shufps/qaxe/nerdqaxe++/nerdqaxe++/3d/csg95472.step

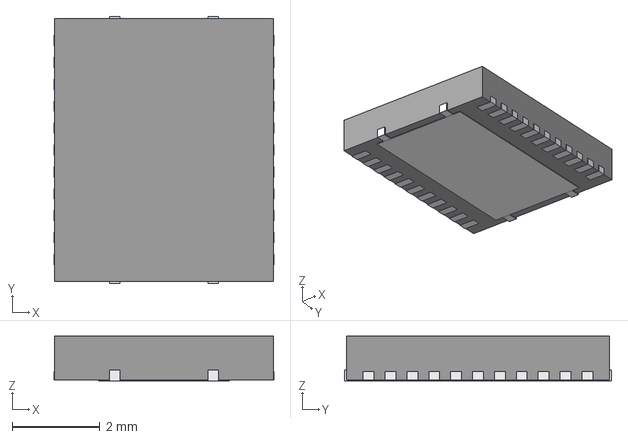
[picture p17: CAD file, 2024-11-11]
nerdqaxe++/nerdqaxe++/3d/csg95472.step
5.02 x 6.10 x 1.02 mm
