shufps/qaxe/nerdqaxe++/nerdqaxe++/bm1366.kicad_sch

## KiCad design nerdqaxe++/nerdqaxe++/bm1366.kicad_sch (2026-01-11)

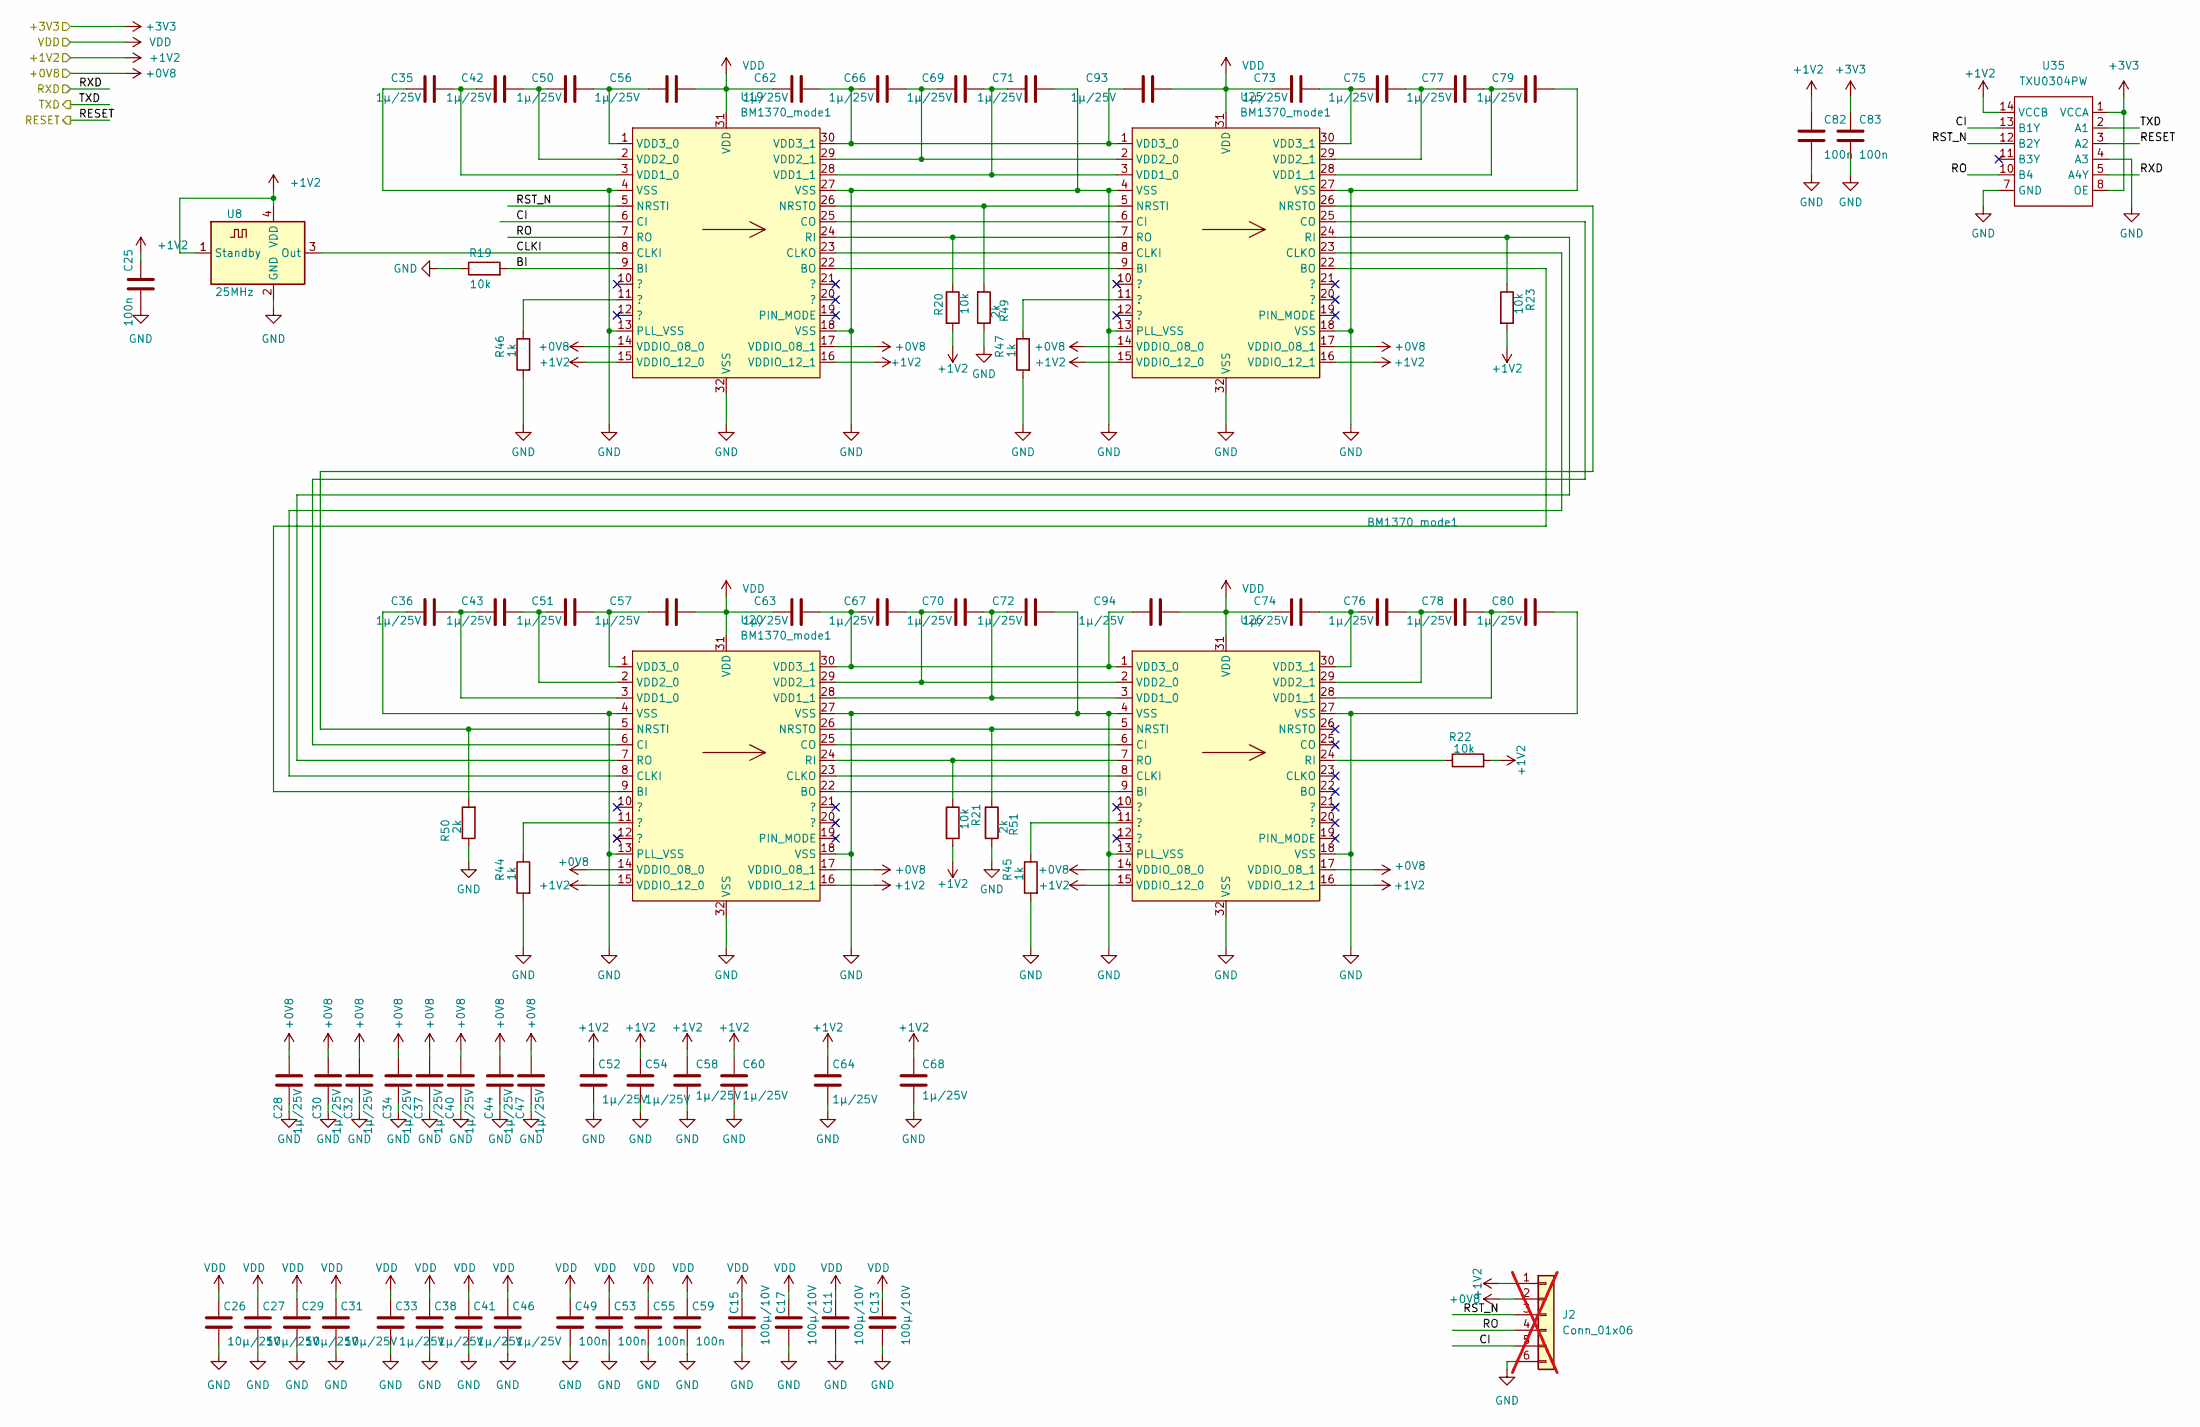
[picture p28: schematic bm1366.kicad_sch]

Parts:
C11, C13, C15, C17: 100µ/10V; C_1210_3225Metric
C25, C49, C53, C55, C59, C82, C83: 100n; C_0805_2012Metric
C26, C27, C29, C31: 10µ/25V; C_0805_2012Metric
C28, C30, C32, C33, C34, C35, C36, C37, C38, C40, C41, C42, C43, C44, C46, C47, C50, C51, C52, C54, C56, C57, C58, C60, C62, C63, C64, C66, C67, C68, C69, C70, C71, C72, C73, C74, C75, C76, C77, C78, C79, C80, C93, C94: 1µ/25V; C_0805_2012Metric
J2: Conn_01x06; PinHeader_1x06_P1.27mm_Vertical; not fitted
R19, R20, R21, R22, R23: 10k; R_0805_2012Metric
R44, R45, R46, R47: 1k; R_0805_2012Metric
R49, R50, R51: 2k; R_0805_2012Metric
U8: 25MHz; Oscillator_SMD_EuroQuartz_XO32-4Pin_3.2x2.5mm
U19, U20, U25, U26: BM1370_mode1; BM1370
U35: TXU0304PW; TSSOP-14_4.4x5mm_P0.65mm

Connections:
+0V8: C28.2, C30.2, C32.2, C34.2, C37.2, C40.2, C44.2, C47.2, J2.2, U19.14 (VDDIO_08_0), U19.17 (VDDIO_08_1), U20.14 (VDDIO_08_0), U20.17 (VDDIO_08_1), U25.14 (VDDIO_08_0), U25.17 (VDDIO_08_1), U26.14 (VDDIO_08_0), U26.17 (VDDIO_08_1)
+1V2: C25.1, C52.1, C54.1, C58.1, C60.1, C64.1, C68.1, C82.1, J2.1, R20.2, R21.2, R22.2, R23.2, U8.1 (Standby), U8.4 (VDD), U19.15 (VDDIO_12_0), U19.16 (VDDIO_12_1), U20.15 (VDDIO_12_0), U20.16 (VDDIO_12_1), U25.15 (VDDIO_12_0), U25.16 (VDDIO_12_1), U26.15 (VDDIO_12_0), U26.16 (VDDIO_12_1), U35.14 (VCCB)
+3V3: C83.1, U35.1 (VCCA), U35.8 (OE)
BI: R19.2, U19.9 (BI)
CI: J2.5, U19.6 (CI), U35.13 (B1Y)
CLKI: U8.3 (Out), U19.8 (CLKI)
GND: C11.2, C13.2, C15.2, C17.2, C25.2, C26.2, C27.2, C28.1, C29.2, C30.1, C31.2, C32.1, C33.2, C34.1, C35.1, C36.1, C37.1, C38.2, C40.1, C41.2, C44.1, C46.2, C47.1, C49.2, C52.2, C53.2, C54.2, C55.2, C58.2, C59.2, C60.2, C64.2, C68.2, C71.2, C72.2, C79.2, C80.2, C82.2, C83.2, J2.6, R19.1, R44.2, R45.2, R46.2, R47.2, R49.1, R50.1, R51.1, U8.2 (GND), U19.4 (VSS), U19.13 (PLL_VSS), U19.18 (VSS), U19.27 (VSS), U19.32 (VSS), U20.4 (VSS), U20.13 (PLL_VSS), U20.18 (VSS), U20.27 (VSS), U20.32 (VSS), U25.4 (VSS), U25.13 (PLL_VSS), U25.18 (VSS), U25.27 (VSS), U25.32 (VSS), U26.4 (VSS), U26.13 (PLL_VSS), U26.18 (VSS), U26.27 (VSS), U26.32 (VSS), U35.4 (A3), U35.7 (GND)
unnamed: C35.2, C42.1, U19.3 (VDD1_0)
unnamed: C36.2, C43.1, U20.3 (VDD1_0)
unnamed: C42.2, C50.1, U19.2 (VDD2_0)
unnamed: C43.2, C51.1, U20.2 (VDD2_0)
unnamed: C50.2, C56.1, U19.1 (VDD3_0)
unnamed: C51.2, C57.1, U20.1 (VDD3_0)
unnamed: C62.2, C66.1, C93.1, U19.30 (VDD3_1), U25.1 (VDD3_0)
unnamed: C63.2, C67.1, C94.1, U20.30 (VDD3_1), U26.1 (VDD3_0)
unnamed: C66.2, C69.1, U19.29 (VDD2_1), U25.2 (VDD2_0)
unnamed: C67.2, C70.1, U20.29 (VDD2_1), U26.2 (VDD2_0)
unnamed: C69.2, C71.1, U19.28 (VDD1_1), U25.3 (VDD1_0)
unnamed: C70.2, C72.1, U20.28 (VDD1_1), U26.3 (VDD1_0)
unnamed: C73.2, C75.1, U25.30 (VDD3_1)
unnamed: C74.2, C76.1, U26.30 (VDD3_1)
unnamed: C75.2, C77.1, U25.29 (VDD2_1)
unnamed: C76.2, C78.1, U26.29 (VDD2_1)
unnamed: C77.2, C79.1, U25.28 (VDD1_1)
unnamed: C78.2, C80.1, U26.28 (VDD1_1)
unnamed: R20.1, U19.24 (RI), U25.7 (RO)
unnamed: R21.1, U20.24 (RI), U26.7 (RO)
unnamed: R22.1, U26.24 (RI)
unnamed: R23.1, U20.7 (RO), U25.24 (RI)
unnamed: R44.1, U20.11 (?)
unnamed: R45.1, U26.11 (?)
unnamed: R46.1, U19.11 (?)
unnamed: R47.1, U25.11 (?)
unnamed: R49.2, U19.26 (NRSTO), U25.5 (NRSTI)
unnamed: R50.2, U20.5 (NRSTI), U25.26 (NRSTO)
unnamed: R51.2, U20.26 (NRSTO), U26.5 (NRSTI)
unnamed: U19.22 (BO), U25.9 (BI)
unnamed: U19.23 (CLKO), U25.8 (CLKI)
unnamed: U19.25 (CO), U25.6 (CI)
unnamed: U20.6 (CI), U25.25 (CO)
unnamed: U20.8 (CLKI), U25.23 (CLKO)
unnamed: U20.9 (BI), U25.22 (BO)
unnamed: U20.22 (BO), U26.9 (BI)
unnamed: U20.23 (CLKO), U26.8 (CLKI)
unnamed: U20.25 (CO), U26.6 (CI)
RESET: U35.3 (A2)
RO: J2.4, U19.7 (RO), U35.10 (B4)
RST_N: J2.3, U19.5 (NRSTI), U35.12 (B2Y)
RXD: U35.5 (A4Y)
TXD: U35.2 (A1)
VDD: C11.1, C13.1, C15.1, C17.1, C26.1, C27.1, C29.1, C31.1, C33.1, C38.1, C41.1, C46.1, C49.1, C53.1, C55.1, C56.2, C57.2, C59.1, C62.1, C63.1, C73.1, C74.1, C93.2, C94.2, U19.31 (VDD), U20.31 (VDD), U25.31 (VDD), U26.31 (VDD)
