shufps/qaxe/nerdqaxe++/nerdqaxe++/nerdqaxe++.kicad_sch

## KiCad design nerdqaxe++/nerdqaxe++/nerdqaxe++.kicad_sch (2026-01-11)

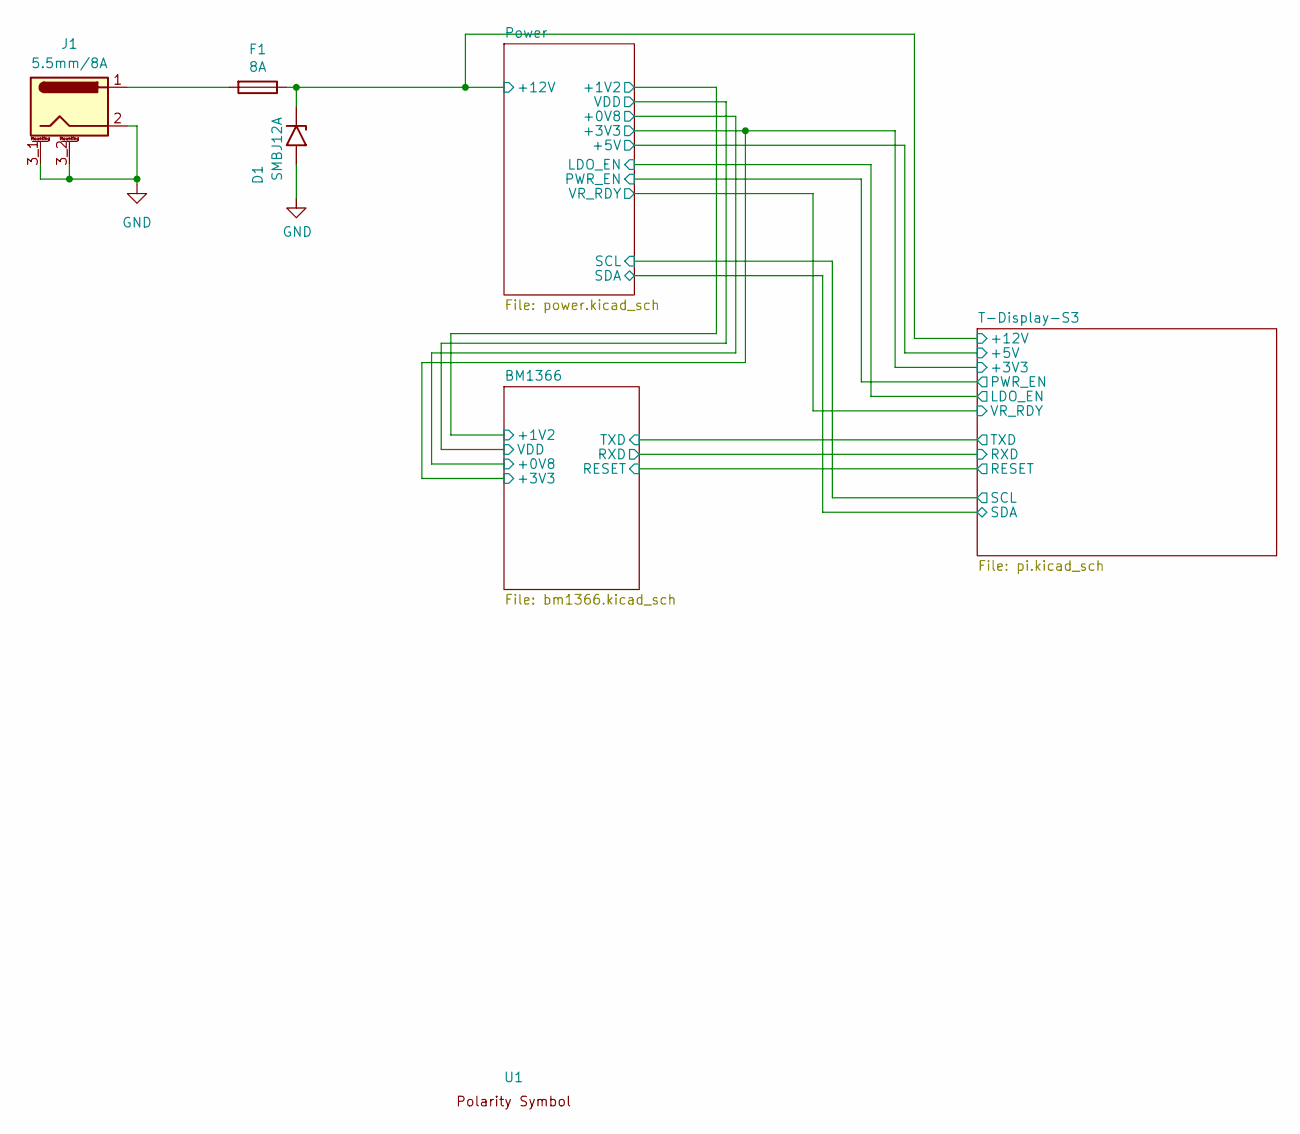
[picture p29: schematic nerdqaxe++.kicad_sch]

Parts:
D1: SMBJ12A; D_SMB
F1: 8A; fuseholder_littlefuse_blok
J1: 5.5mm/8A; GCT_DCJ250-20-B-XX-X_REVA1
U1: polarity

Connections:
+12V: D1.1 (A1), F1.1
GND: D1.2 (A2), J1.2, J1.3_1 (MountPin), J1.3_2 (MountPin)
unnamed: F1.2, J1.1
