shufps/qaxe/nerdqaxe++/nerdqaxe++/power-stage.kicad_sch

## KiCad design nerdqaxe++/nerdqaxe++/power-stage.kicad_sch (2026-01-15)

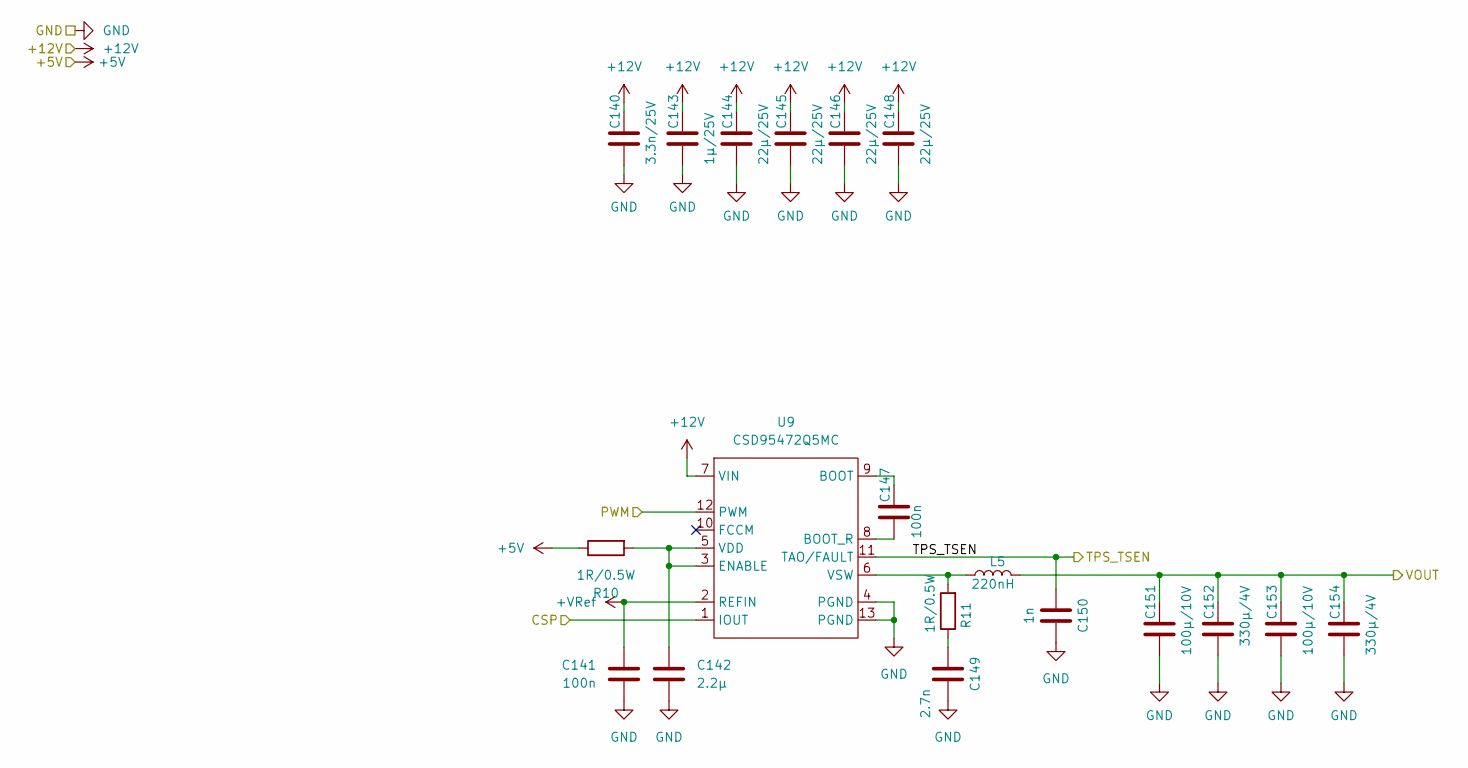
[picture p31: schematic power-stage.kicad_sch]

Parts:
C140: 3.3n/25V; C_0805_2012Metric
C141, C147: 100n; C_0805_2012Metric
C142: 2.2µ; C_0805_2012Metric
C143: 1µ/25V; C_0805_2012Metric
C144, C145, C146, C148: 22µ/25V; C_1210_3225Metric
C149: 2.7n; C_0805_2012Metric
C150: 1n; C_0805_2012Metric
C151, C153: 100µ/10V; C_1210_3225Metric
C152, C154: 330µ/4V; C_1210_3225Metric
L5: 220nH; IFLR-4031GC-01-8x10
R10, R11: 1R/0.5W; R_0805_2012Metric
U9: CSD95472Q5MC; CSD95472-SON-5x6

Connections:
+5V: R10.1
+12V: C140.1, C143.1, C144.1, C145.1, C146.1, C148.1, U9.7 (VIN)
+VRef: C141.1, U9.2 (REFIN)
CSP: U9.1 (IOUT)
GND: C140.2, C141.2, C142.2, C143.2, C144.2, C145.2, C146.2, C148.2, C149.2, C150.2, C151.2, C152.2, C153.2, C154.2, U9.4 (PGND), U9.13 (PGND)
unnamed: C142.1, R10.2, U9.3 (ENABLE), U9.5 (VDD)
unnamed: C147.1, U9.9 (BOOT)
unnamed: C147.2, U9.8 (BOOT_R)
unnamed: C149.1, R11.1
unnamed: L5.1, R11.2, U9.6 (VSW)
PWM: U9.12 (PWM)
TPS_TSEN: C150.1, U9.11 (TAO/FAULT)
VOUT: C151.1, C152.1, C153.1, C154.1, L5.2
