shufps/qaxe/nerdqaxe++/nerdqaxe++/power.kicad_sch

## KiCad design nerdqaxe++/nerdqaxe++/power.kicad_sch (2026-01-15)

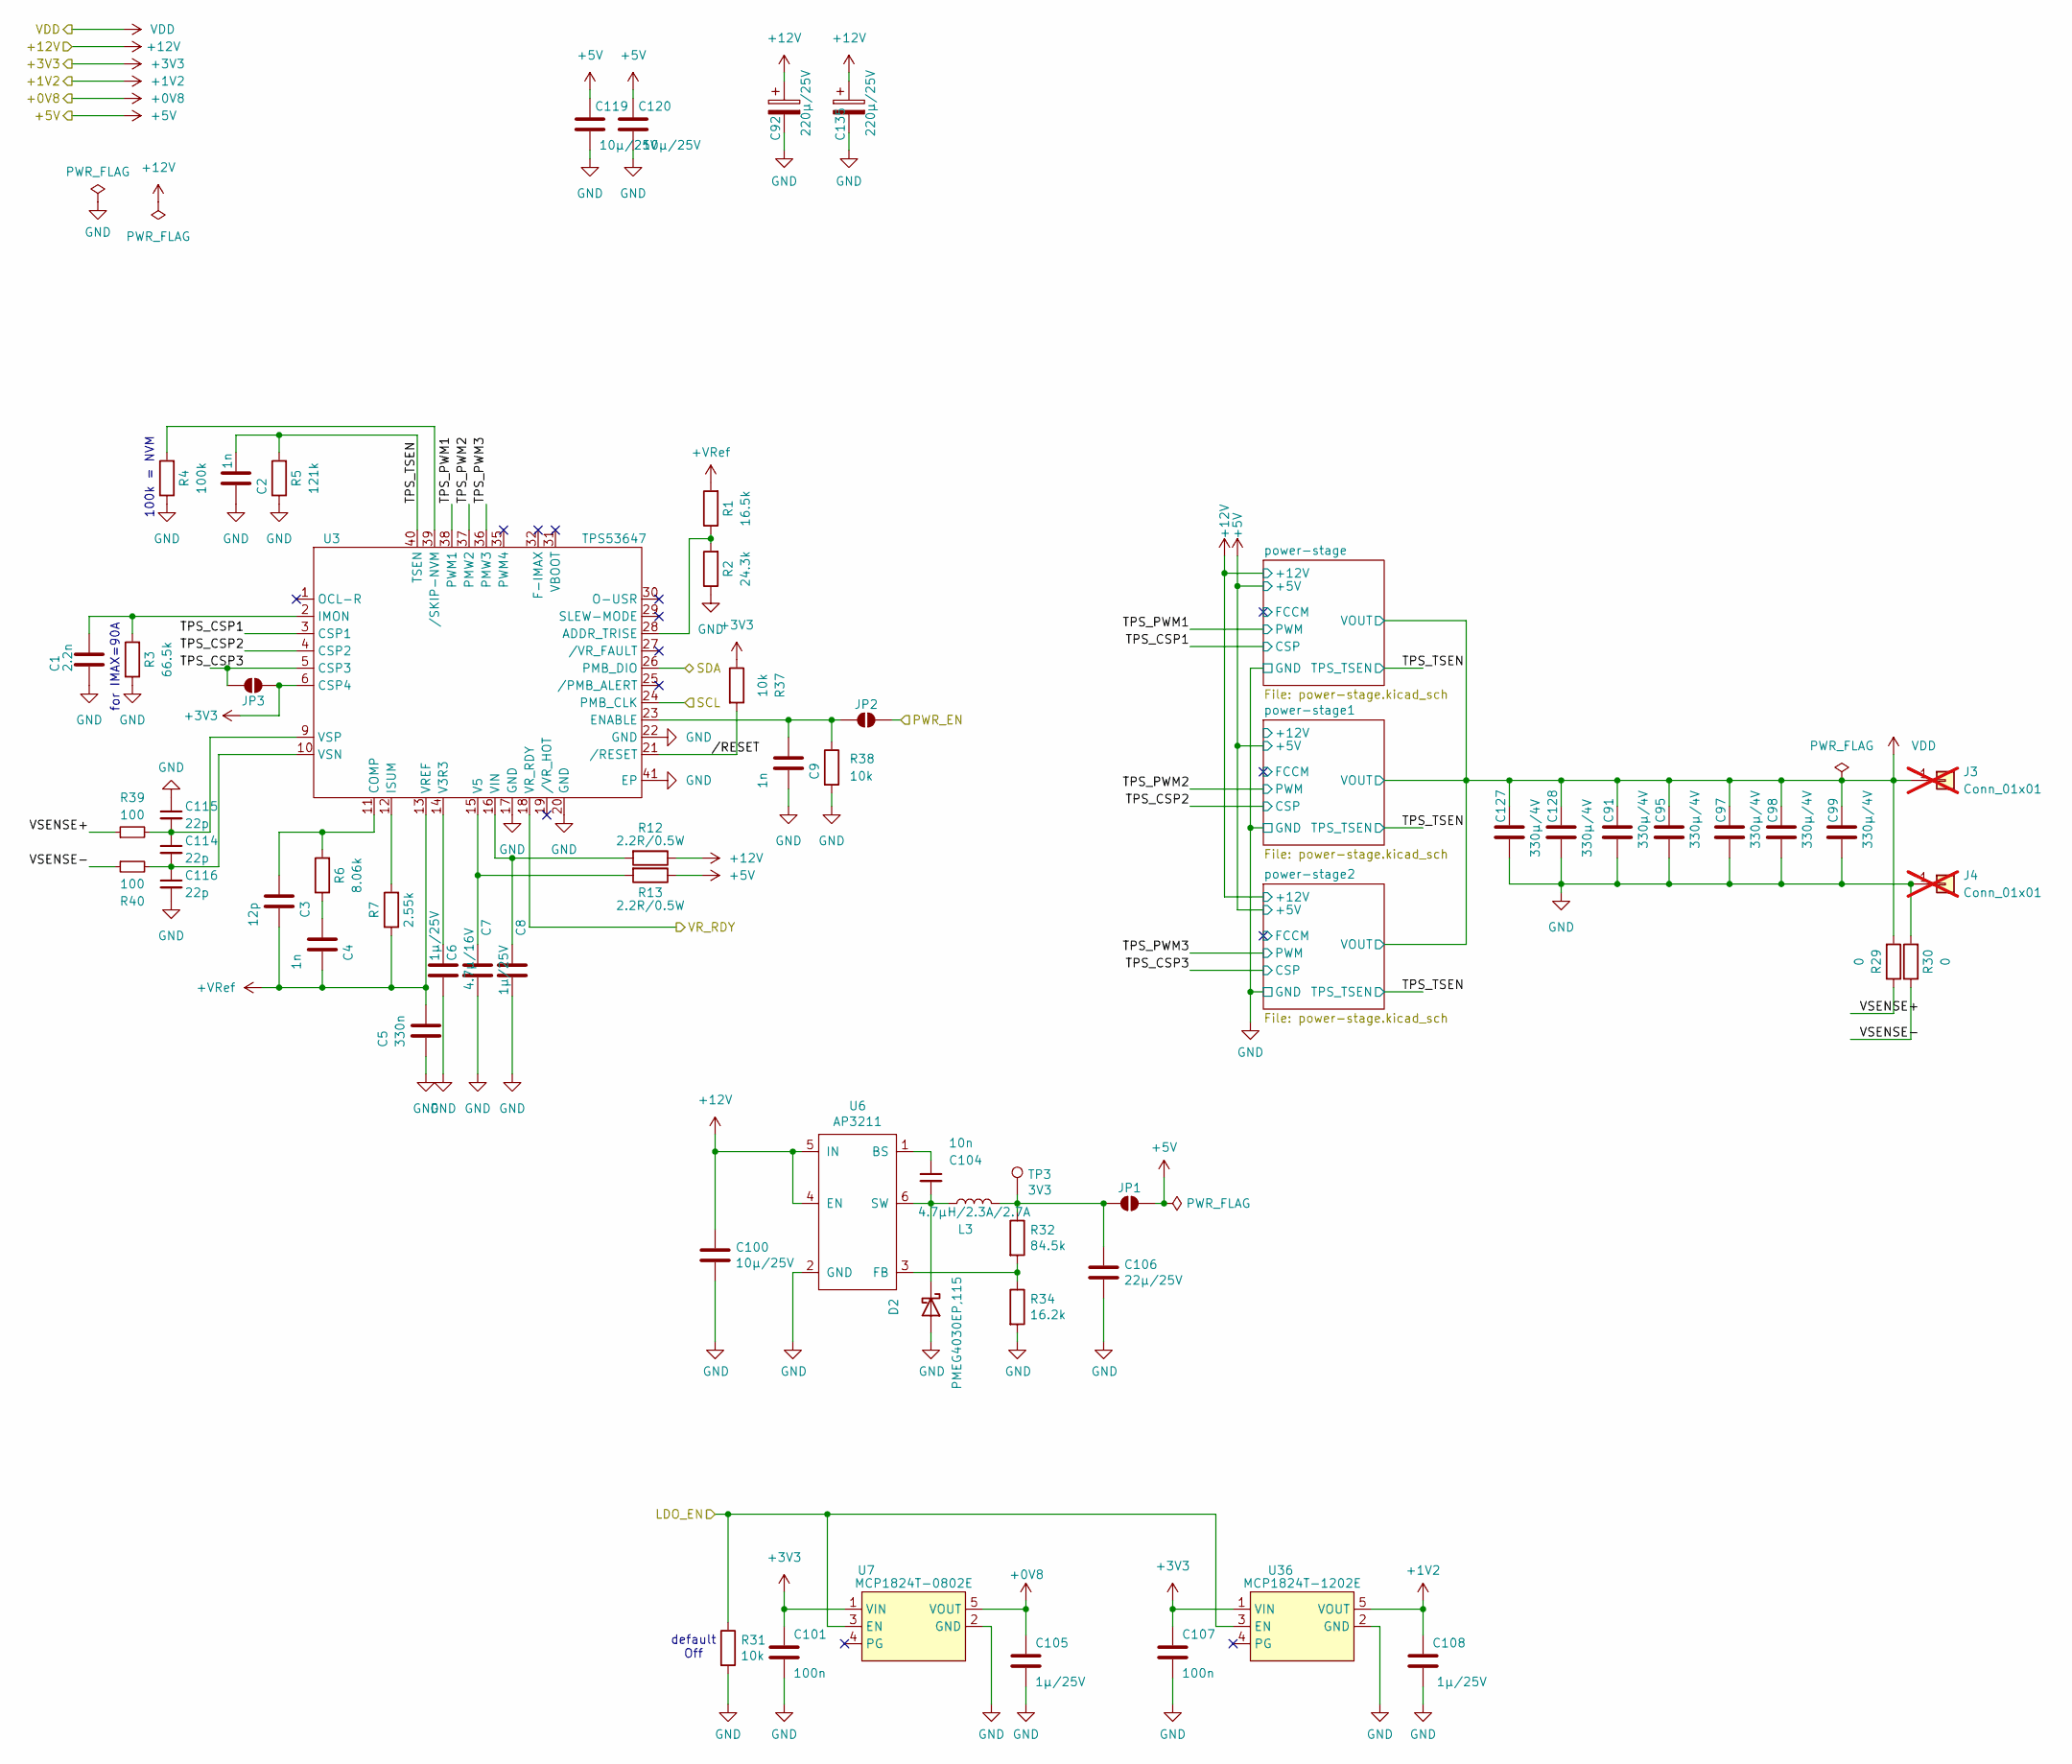
[picture p32: schematic power.kicad_sch]

Parts:
C1: 2.2n; C_0805_2012Metric
C2, C4, C9: 1n; C_0805_2012Metric
C3: 12p; C_0603_1608Metric
C5: 330n; C_0805_2012Metric
C6, C8, C105, C108: 1µ/25V; C_0805_2012Metric
C7: 4.7µ/16V; C_0805_2012Metric
C91, C95, C97, C98, C99, C127, C128: 330µ/4V; C_1210_3225Metric
C92, C135: 220µ/25V; CP_Elec_8x10
C100, C119, C120: 10µ/25V; C_0805_2012Metric
C101, C107: 100n; C_0805_2012Metric
C104: 10n; C_0805_2012Metric
C106: 22µ/25V; C_1210_3225Metric
C114, C115, C116: 22p; C_0603_1608Metric
D2: PMEG4030EP,115; D_SOD-128
J3, J4: Conn_01x01; Wuerth_REDCUBE-THR_WP-THRBU_74650194_THR; not fitted
JP1, JP2, JP3: SolderJumper_2_Open; SolderJumper-2_P1.3mm_Open_RoundedPad1.0x1.5mm
L3: 4.7µH/2.3A/2.7A; L_Taiyo-Yuden_NR-50xx
R1: 16.5k; R_0805_2012Metric
R2: 24.3k; R_0805_2012Metric
R3: 66.5k; R_0805_2012Metric
R4: 100k; R_0805_2012Metric
R5: 121k; R_0805_2012Metric
R6: 8.06k; R_0805_2012Metric
R7: 2.55k; R_0805_2012Metric
R12, R13: 2.2R/0.5W; R_0805_2012Metric
R29, R30: 0; R_0805_2012Metric
R31, R37, R38: 10k; R_0805_2012Metric
R32: 84.5k; R_0805_2012Metric
R34: 16.2k; R_0805_2012Metric
R39, R40: 100; R_0805_2012Metric
TP3: 3V3; TestPoint_Pad_2.0x2.0mm
U3: TPS53647; Texas_RHA0040B_VQFN-40-1EP_6x6mm_P0.5mm_EP4.15x4.15mm_Therm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
U6: AP3211; SOT-23-6
U7: MCP1824T-0802E; SOT-23-5
U36: MCP1824T-1202E; SOT-23-5

Connections:
+0V8: C105.1, U7.5 (VOUT)
+1V2: C108.1, U36.5 (VOUT)
+3V3: C101.1, C107.1, JP3.2 (B), R37.1, U3.6 (CSP4), U7.1 (VIN), U36.1 (VIN)
+5V: C119.1, C120.1, JP1.2 (B), R13.1
+12V: C92.1, C100.1, C135.1, R12.1, U6.4 (EN), U6.5 (IN)
+VRef: C3.2, C4.2, C5.1, R1.2, R7.1, U3.13 (VREF)
GND: C1.2, C2.2, C5.2, C6.2, C7.1, C8.1, C9.2, C91.2, C92.2, C95.2, C97.2, C98.2, C99.2, C100.2, C101.2, C105.2, C106.2, C107.2, C108.2, C115.1, C116.2, C119.2, C120.2, C127.2, C128.2, C135.2, D2.2 (A), J4.1, R2.1, R3.1, R4.1, R5.1, R30.2, R31.2, R34.2, R38.2, U3.17 (GND), U3.20 (GND), U3.22 (GND), U3.41 (EP), U6.2 (GND), U7.2 (GND), U36.2 (GND)
LDO_EN: R31.1, U7.3 (EN), U36.3 (EN)
unnamed: C1.1, R3.2, U3.2 (IMON)
unnamed: C3.1, R6.2, U3.11 (COMP)
unnamed: C4.1, R6.1
unnamed: C6.1, U3.14 (V3R3)
unnamed: C7.2, R13.2, U3.15 (V5)
unnamed: C8.2, R12.2, U3.16 (VIN)
unnamed: C9.1, JP2.1 (A), R38.1, U3.23 (ENABLE)
unnamed: C104.1, U6.1 (BS)
unnamed: C104.2, D2.1 (K), L3.1, U6.6 (SW)
unnamed: C106.1, JP1.1 (A), L3.2, R32.1, TP3.1
unnamed: C114.1, C115.2, R39.2, U3.9 (VSP)
unnamed: C114.2, C116.1, R40.2, U3.10 (VSN)
unnamed: R1.1, R2.2, U3.28 (ADDR_TRISE)
unnamed: R4.2, U3.39 (/SKIP-NVM)
unnamed: R7.2, U3.12 (ISUM)
unnamed: R32.2, R34.1, U6.3 (FB)
PWR_EN: JP2.2 (B)
SCL: U3.24 (PMB_CLK)
SDA: U3.26 (PMB_DIO)
TPS_CSP1: U3.3 (CSP1)
TPS_CSP2: U3.4 (CSP2)
TPS_CSP3: JP3.1 (A), U3.5 (CSP3)
TPS_PWM1: U3.38 (PWM1)
TPS_PWM2: U3.37 (PMW2)
TPS_PWM3: U3.36 (PMW3)
TPS_TSEN: C2.1, R5.2, U3.40 (TSEN)
VDD: C91.1, C95.1, C97.1, C98.1, C99.1, C127.1, C128.1, J3.1, R29.2
VR_RDY: U3.18 (VR_RDY)
VSENSE+: R29.1, R39.1
VSENSE-: R30.1, R40.1
/RESET: R37.2, U3.21 (/RESET)

Notes on the sheet:
default Off
for IMAX=90A
100k = NVM
